kushmdesai/Ulti-Board/journal/Images/fullcasedesign.png

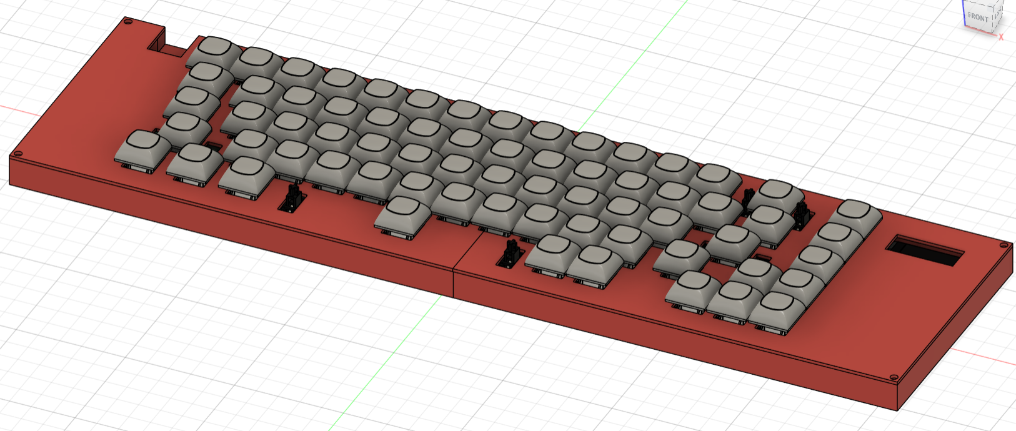
journal/Images/fullcasedesign.png
